tlon-citizen/HapGloves/Sketch/board.sch

## EAGLE design Sketch/board.sch (2020-12-28)

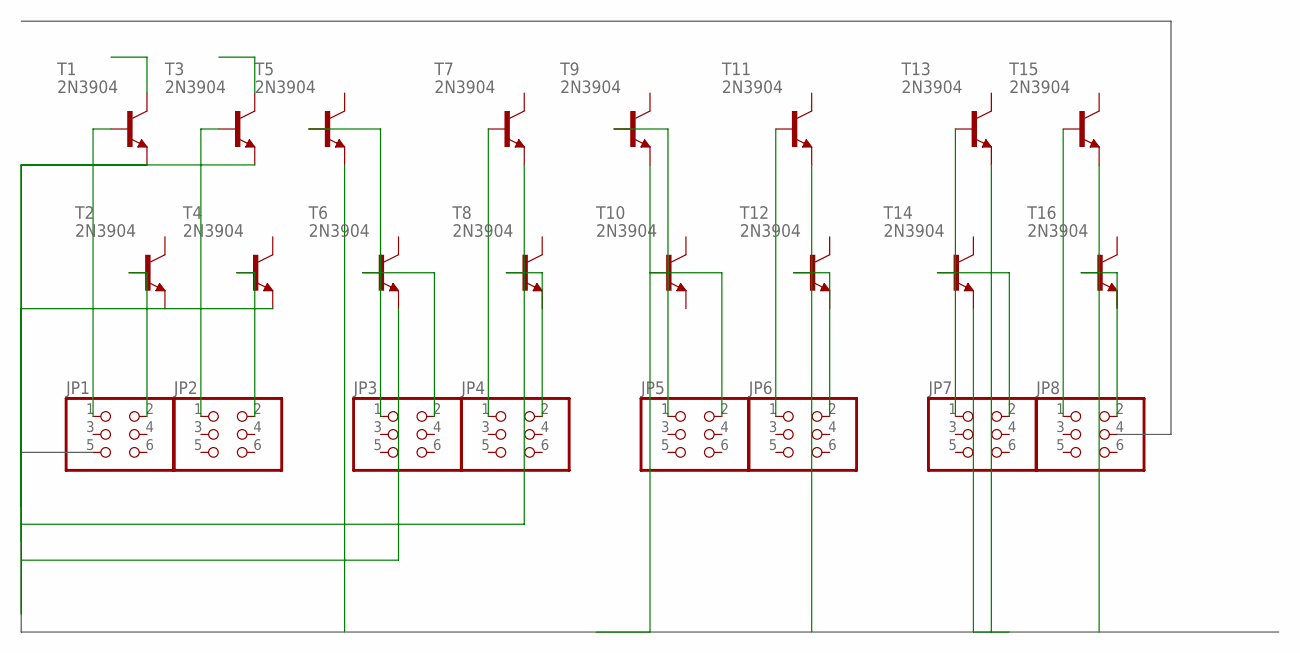
[picture p4: schematic board.sch]

Parts:
JP1, JP2, JP3, JP4, JP5, JP6, JP7, JP8: PINHD-2X3; 2X03
T1, T2, T3, T4, T5, T6, T7, T8, T9, T10, T11, T12, T13, T14, T15, T16: 2N3904; TO92

Connections:
B$1: T1.3 (E), T3.3 (E), T4.3 (E), T5.3 (E), T6.3 (E), T7.3 (E), T9.3 (E), T11.3 (E), T13.3 (E), T14.3 (E), T15.3 (E)
unnamed: JP1.1, T1.2 (B)
unnamed: JP1.2, T2.2 (B)
unnamed: JP2.1, T3.2 (B)
unnamed: JP2.2, T4.2 (B)
unnamed: JP3.1, T5.2 (B)
unnamed: JP3.2, T6.2 (B)
unnamed: JP4.1, T7.2 (B)
unnamed: JP4.2, T8.2 (B)
unnamed: JP5.1, T9.2 (B)
unnamed: JP5.2, T10.2 (B)
unnamed: JP6.1, T11.2 (B)
unnamed: JP6.2, T12.2 (B)
unnamed: JP7.1, T13.2 (B)
unnamed: JP7.2, T14.2 (B)
unnamed: JP8.1, T15.2 (B)
unnamed: JP8.2, T16.2 (B)
